jmwilson/leave-time-behind/CAD files/rendering.jpg

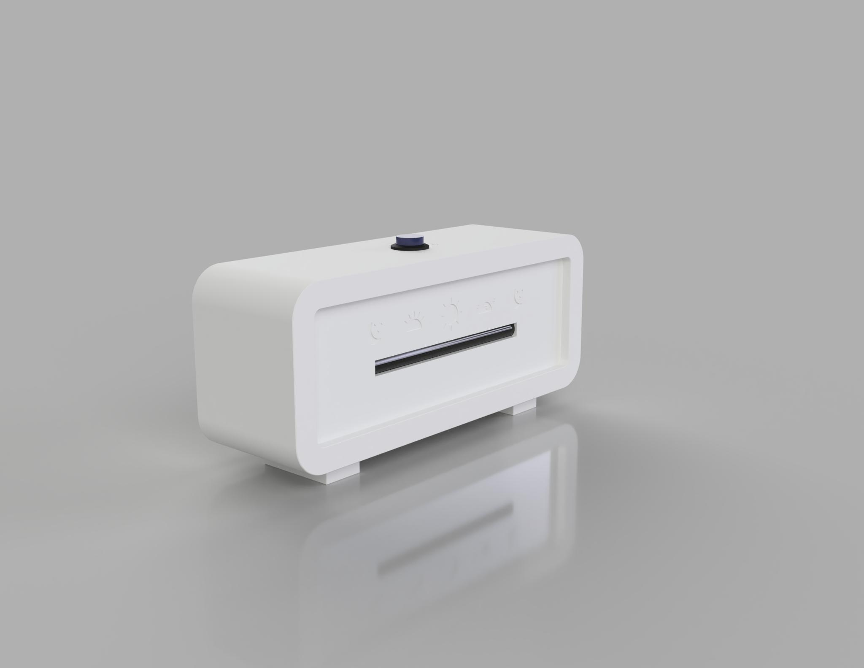
CAD files/rendering.jpg
