jmwilson/leave-time-behind/Scope captures/Rev B/scope_1.png

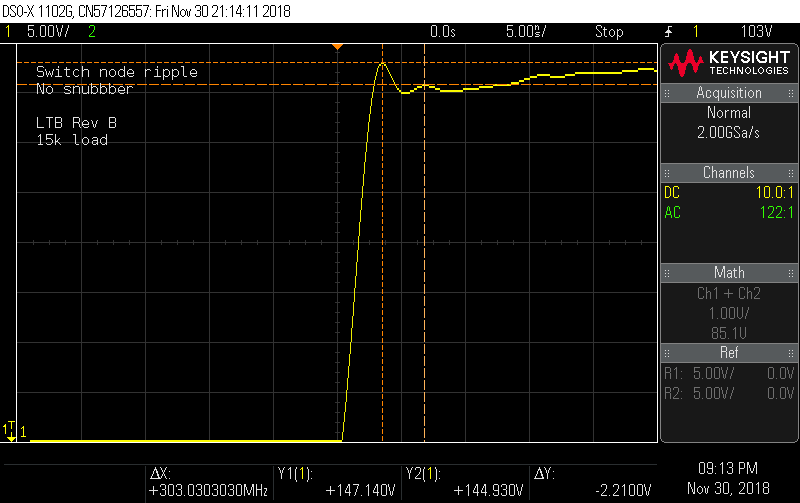
Scope captures/Rev B/scope_1.png
