jmwilson/leave-time-behind/Scope captures/Rev B/scope_2.png

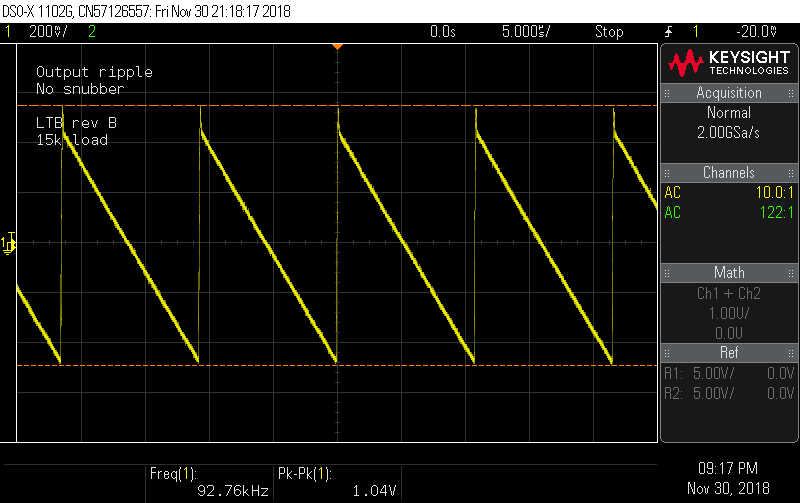
Scope captures/Rev B/scope_2.png
