jmwilson/leave-time-behind/Scope captures/Rev B/scope_3.png

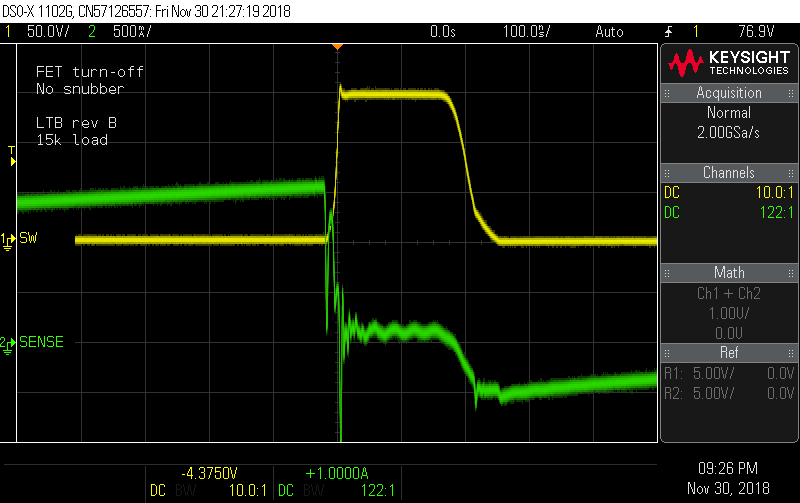
Scope captures/Rev B/scope_3.png
