jmwilson/leave-time-behind/Scope captures/Rev B/scope_4.png

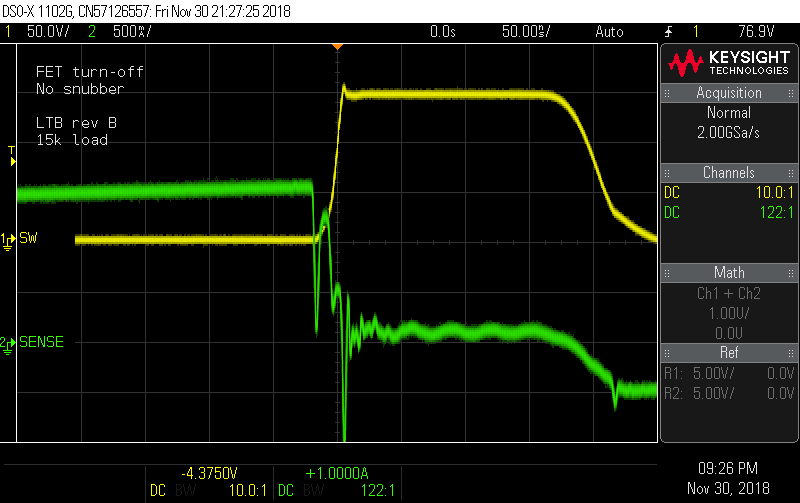
Scope captures/Rev B/scope_4.png
