jmwilson/leave-time-behind/Scope captures/Rev B/scope_5.png

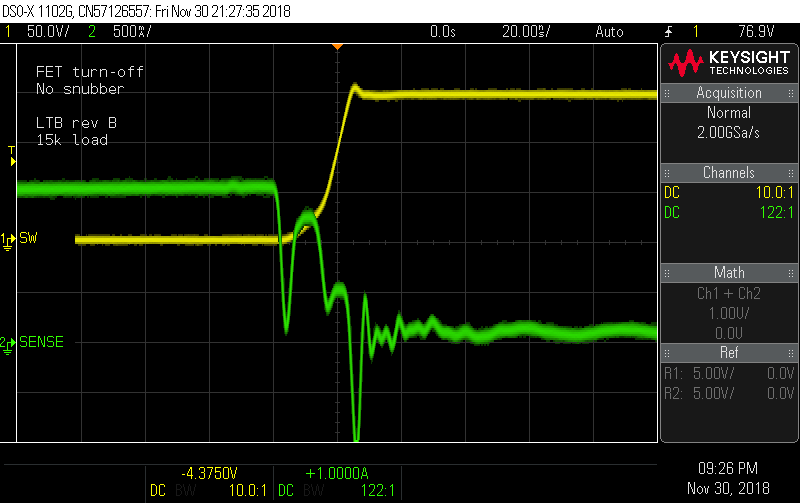
Scope captures/Rev B/scope_5.png
