jmwilson/leave-time-behind/Scope captures/Rev B/scope_6.png

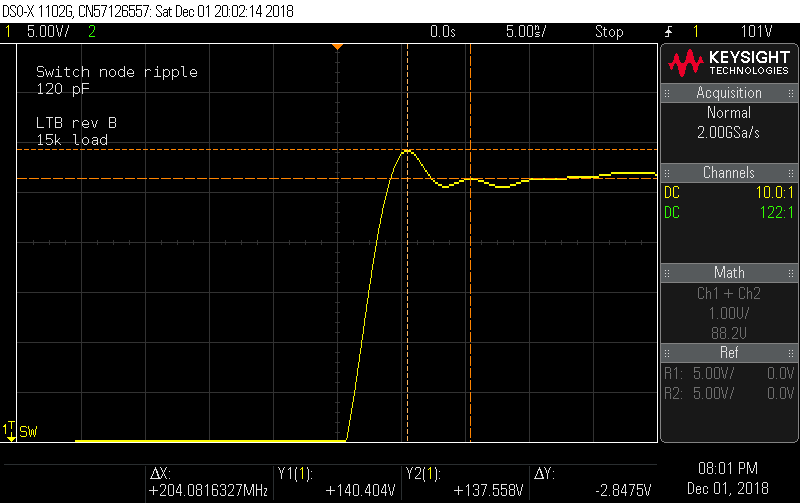
Scope captures/Rev B/scope_6.png
