jmwilson/leave-time-behind/Scope captures/Rev B/scope_9.png

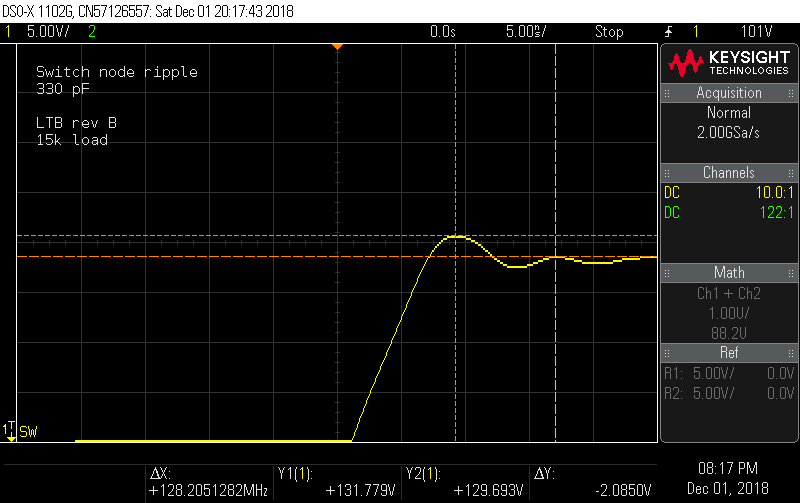
Scope captures/Rev B/scope_9.png
