jmwilson/leave-time-behind/Scope captures/Rev B/scope_10.png

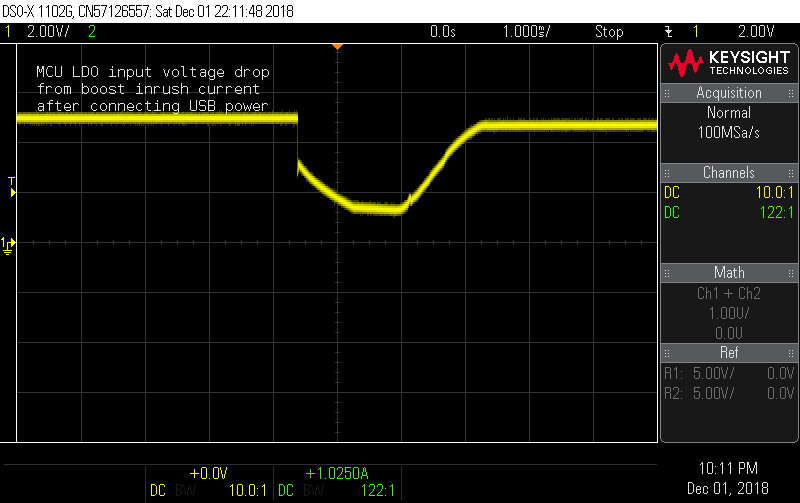
Scope captures/Rev B/scope_10.png
