jmwilson/leave-time-behind/Scope captures/Rev B/scope_11.png

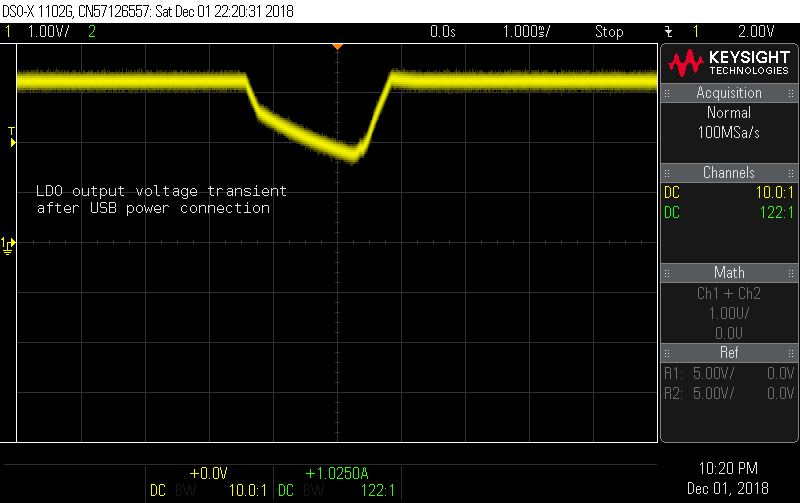
Scope captures/Rev B/scope_11.png
