jmwilson/leave-time-behind/Scope captures/Rev B/scope_13.png

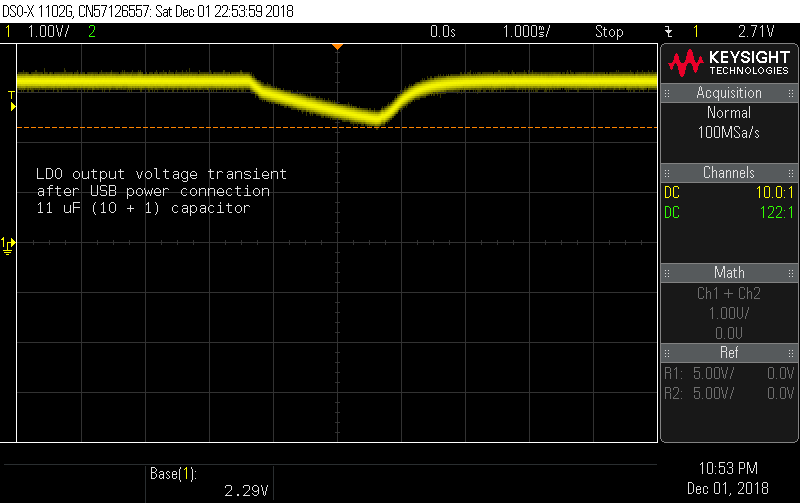
Scope captures/Rev B/scope_13.png
