jmwilson/leave-time-behind/Scope captures/Rev B/scope_17.png

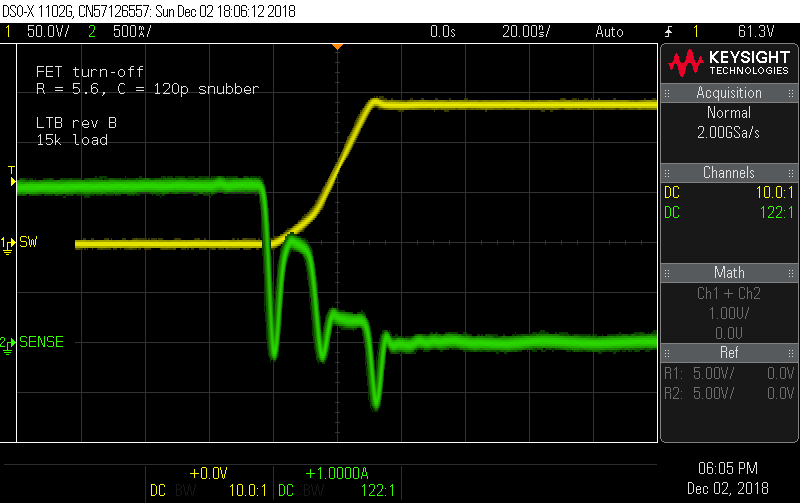
Scope captures/Rev B/scope_17.png
