jmwilson/leave-time-behind/Scope captures/Rev B/scope_20.png

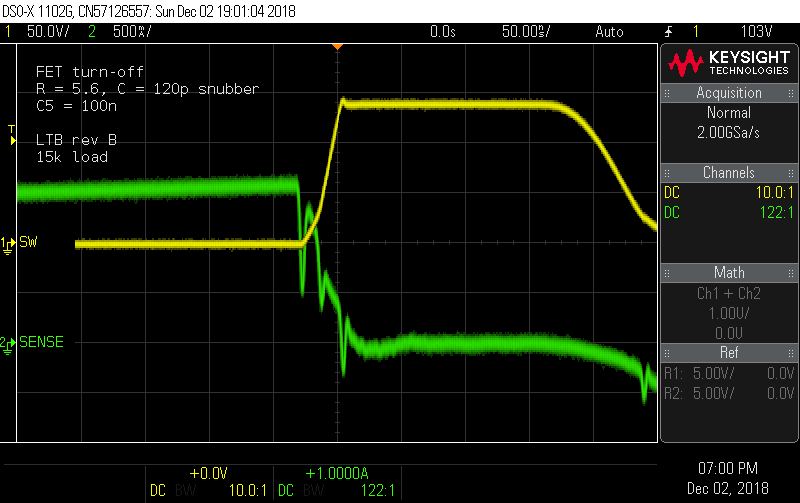
Scope captures/Rev B/scope_20.png
