jmwilson/leave-time-behind/spice/DCM CPM average CL.asc

C1: cap; 100n
C2: cap; 5.6n
C3: cap; 22µ; Rser=100m
C4: cap; 100µ; Rser=45m
E1: e; 1
E2: e; 1
G1: g2; 800µ; table=(-.175, -140u) (.138, 110u)
Hsense1: h; value={Rf*i(L1)}
I1: current; PULSE(0 5m 3m 10u 10u 1m 10m 1)
L1: ind; {Lb}; Rser=90m
L2: ind; 10µ; Rser=50m
R1: res; {Rload}
R2: res; 200m
R3: res; 1.5Meg
R4: res; 12.7k
R5: res; 4.3k
R6: res; 500m
Rout: res; 47.5k
U2: cpm; CPM-DCM; Rf={Rf} Va={VSL}
U3: ccm-dcm1; L={Lb} fs={fs}
V3: voltage; ""; AC 1
Vg1: voltage; {Vin}; Rser=30m
Vref: voltage; 1.26; Rser=100
Named nets: 0, in, out, x, y
.lib switching.lib
.lib average.lib
;.tran 5m startup uic
.param Rf=41m fs=100k Lb=15u Vin=5 Vout=150 Rload=15k
.param VSL=111m
.lib cpm-dcm.lib
.ac dec 300 1 1Meg
.meas AC crossover FIND -v(y)/v(x) WHEN mag(-v(y)/v(x))=1
;.step param Rload list 6k 15k 30k
