jmwilson/leave-time-behind/spice/DCM CPM average.asc

C1: cap; 100n
E1: e; 1
E2: e; 1
Hsense1: h; value={Rf*i(L1)}
I1: current; {Vout*(1+(VSL*fs)/(Rf*Vin/Lb))*sqrt((1-Vin/Vout)*2/(Lb*Rload*fs))}; AC 1
L1: ind; {Lb}; Rser=90m
R1: res; {Rload}
R2: res; {Rf}
U1: cpm; CPM-DCM; Rf={Rf} Va={VSL}
U2: ccm-dcm1; L={Lb} fs={fs}
Vg: voltage; {Vin}
Named nets: 0, in, out
.lib switching.lib
.lib average.lib
.tran 20m uic
;ac dec 300 1 1Meg
.param Rf=82m fs=100k Lb=15u Vin=5 Vout=150 Rload=15k
.param ma={(Vout-Vin)/Lb} VSL=92m
.op
.lib cpm-dcm.lib
