jmwilson/leave-time-behind/spice/DCM CPM LM3478.asc

C1: cap; 10µ
C2: cap; 100n; Rser=20m
C3: cap; 5.6n
C4: cap; 100n
C5: cap; 470n
C6: cap; 22µ; Rser=100m
C7: cap; 100µ; Rser=45m
C9: cap; 1n
C10: cap; 100p
D1: diode; STPS2200UF
L1: ind; 15µ; Rser=90m
L2: ind; 10µ; Rser=50m
L3: ind; 3n
L4: ind; 2n
L7: ind; 50p
M1: nmos; BSZ900N20NS3_L0
Q1: npn; 2N3904
R1: res; 20
R2: res; 1.5Meg
R3: res; 500m
R4: res; 39m
R5: res; 12.7k
R6: res; 4.3k
R7: res; 200m
R8: res; 5.6
R9: res; 180k
R10: res; 0
R11: res; 47k
R12: res; 68k
R13: res; 12k
Rload: res; 15k
U1: LM3478_TRANS
Vin: voltage; 5; Rser=30m
Named nets: 0, Vout, COMP, VIN
.tran 100m startup
.include ST_POWER_SCHOTTKY_V6.mdl
.lib OptiMOS3_200V.lib
External soft-start
