jmwilson/leave-time-behind/spice/DCM CPM switching CL.asc

C1: cap; 100n
C2: cap; 4.7n
C3: cap; 560p
C5: cap; 10µ
C6: cap; 22µ; Rser=100m
C7: cap; 100µ; Rser=45m
D1: schottky; STPS2200UF
G1: g2; 800µ; table=(-.175, -140u) (.138, 110u)
I2: current; PULSE(0 5m 3m 10u 10u 1m 10m 1)
L1: ind; VLS6045EX_150M_s; Rser=75m
L2: ind; VLS6045EX_100M_s; Rser=50m
L3: ind; 2n
L4: ind; 2n
L5: ind; 2n
L6: ind; 2n
L7: ind; 2n
L8: ind; 50p
M1: nmos; BSZ900N20NS3_L0
R1: res; 500m
R2: res; {Rf}
R3: res; 11k
R4: res; 1.5Meg
R5: res; 12.7k
R6: res; 200m
R7: res; 1
R8: res; {Rload}
R9: res; 10
Rout1: res; 47.5k
U1: CPM_modulator; fs={fs}, Va={VSL}
Vg1: voltage; {Vin}; Rser=10m
Vref1: voltage; 1.26; Rser=100
Named nets: 0, in, out, Isen, ramp
.lib switching.lib
.lib average.lib
.tran 0 1.5m 1m uic
.param Rf=82m fs=100k Lb=15u Vin=5 Vout=150 Rload=33k
.param VSL=92m
.lib ST_POWER_SCHOTTKY_V6.mdl
.meas TRAN Pin AVG -v(in)*I(Vg1) FROM .4m TO .5m
.meas TRAN Pout AVG v(out)*I(R8) FROM .4m TO .5m
.meas TRAN Eff PARAM 100*Pout/Pin
.lib OptiMOS3_200V.lib
.lib VLS6045EX_100M_s.mod
.lib VLS6045EX_150M_s.mod
;.step param Csnub list 0 270p 470p
.param Csnub 330p
