jmwilson/leave-time-behind/spice/DCM CPM switching.asc

C1: cap; 100n
D1: diode
I1: current; {Vout*(1+(VSL*fs)/(Rf*Vin/Lb))*sqrt((1-Vin/Vout)*2/(Lb*Rload*fs))}
L1: ind; {Lb}; Rser=90m
M1: nmos; BSC600N25NS3
R1: res; {Rload}
R2: res; {Rf}
R3: res; {Rf}
U3: CPM_modulator; fs={fs}, Va={VSL}
Vg1: voltage; {Vin}
Named nets: 0, in, out, Isen, ramp
.lib switching.lib
.lib average.lib
.tran 20m startup uic
.param Rf=85m fs=100k Lb=15u Vin=5 Vout=150 Rload=15k
.param ma={(Vout-Vin)/Lb} VSL=92m
