jmwilson/leave-time-behind/spice/emi_filter.asc

C1: cap; 22µ; Rser=100m
Cd: cap; 100µ; Rser=45m
L1: ind; 10µ; Rser=50m
R1: res; 200m
R2: res; 500m
V2: voltage; ""; AC 1
Named nets: 0
.ac dec 300 10 1Meg
