jmwilson/leave-time-behind/spice/Nixie driver.asc

C1: cap; 47n
C2: cap; 100n
Q1: nmos; nvmfd5877nlt1g
Q2: nmos; nvmfd5877nlt1g
R1: res; 56
R2: res; 18k
R3: res; 2k
R4: res; 3k
R5: res; 300k
R6: res; 180k
R7: res; 330k
R8: res; 30k
R9: res; 16
R10: res; 100k
U1: TLV9062
U2: TLV9062
V1: voltage; PULSE(0 3.3 0 100n 100n 76u 100u); Rser=100
V2: voltage; 150
V3: voltage; 4.7
V4: voltage; 96
V5: voltage; ""; AC 1
V6: voltage; 96
Named nets: 0
.tran 200m startup uic
.lib small_signal_60V.lib
.lib tlv9062.lib
;ac dec 300 10 1Meg
Sallen-Key 2-pole filter
Butterworth design Q=.707
Break frequency 10 Hz
Nixie Tube modeled as voltage source
IN-13 datasheet has anode-cathode voltage of 94-99 V
Optional R4 reduces Vds of Q1 for most operating points
Constant current driver
for maximum (R3 / (R2 + R3)) * 3.3 V / R1 = 4.6 mA
3.3 V 10 kHz PWM logic signal
Auxilliary cathode soft-start drives Q2 gate with 4.5 V when current is .15 mA
.lib NVMFD5877NL.LIB
