jmwilson/leave-time-behind/firmware/nrf_calendar.c

/**
 * Copyright (c) 2018 James Wilson
 * All rights reserved.
 *
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
 * You should have received a copy of the GNU General Public License
 * along with this program.  If not, see <https://www.gnu.org/licenses/>.
 */

#include <stdint.h>

#include "nrf_calendar.h"
#include "nrfx_clock.h"
#include "nrfx_rtc.h"

#define RTC_INCREMENT 60

static time_t m_time;
static nrfx_rtc_t rtc_inst = NRFX_RTC_INSTANCE(2);

static void cal_rtc_handler(nrfx_rtc_int_type_t int_type)
{
    if (int_type == NRFX_RTC_INT_COMPARE0) {
        nrfx_rtc_counter_clear(&rtc_inst);
        m_time += RTC_INCREMENT;
    }
}

static void clock_handler(nrfx_clock_evt_type_t event)
{
}

void nrf_cal_init(void)
{
    uint32_t err_code;

    err_code = nrfx_clock_init(clock_handler);
    if (err_code != NRFX_ERROR_ALREADY_INITIALIZED) {
        APP_ERROR_CHECK(err_code);
        nrfx_clock_lfclk_start();
    }
    while (!nrfx_clock_lfclk_is_running()) {}

    nrfx_rtc_config_t config = NRFX_RTC_DEFAULT_CONFIG;
    config.prescaler = 4095;  // 8 Hz = 32 kHz / (prescaler + 1)
    config.interrupt_priority = APP_IRQ_PRIORITY_HIGHEST;
    err_code = nrfx_rtc_init(&rtc_inst, &config, cal_rtc_handler);
    APP_ERROR_CHECK(err_code);
    nrfx_rtc_tick_disable(&rtc_inst);
    // Compare counter will rollover every 60 s
    err_code = nrfx_rtc_cc_set(&rtc_inst, 0, RTC_INCREMENT * 8, true);
    APP_ERROR_CHECK(err_code);
    nrfx_rtc_enable(&rtc_inst);
}

void nrf_cal_set_time(uint32_t year, uint32_t month, uint32_t day, uint32_t hour, uint32_t minute, uint32_t second)
{
    time_t newtime;
    struct tm time_struct;

    time_struct.tm_year = year - 1900;
    time_struct.tm_mon = month - 1;
    time_struct.tm_mday = day;
    time_struct.tm_hour = hour;
    time_struct.tm_min = minute;
    time_struct.tm_sec = second;
    newtime = mktime(&time_struct);

    nrfx_rtc_counter_clear(&rtc_inst);
    m_time = newtime;
}

struct tm *nrf_cal_get_time(void)
{
    time_t return_time;
    return_time = m_time + nrfx_rtc_counter_get(&rtc_inst) / 8;
    return localtime(&return_time);
}

char *nrf_cal_get_time_string(void)
{
    static char cal_string[80];
    strftime(cal_string, 80, "%F %T", nrf_cal_get_time());
    return cal_string;
}
